Franklingo13/Efecto-dopler/Piezas/medidas_pieza1.bmp

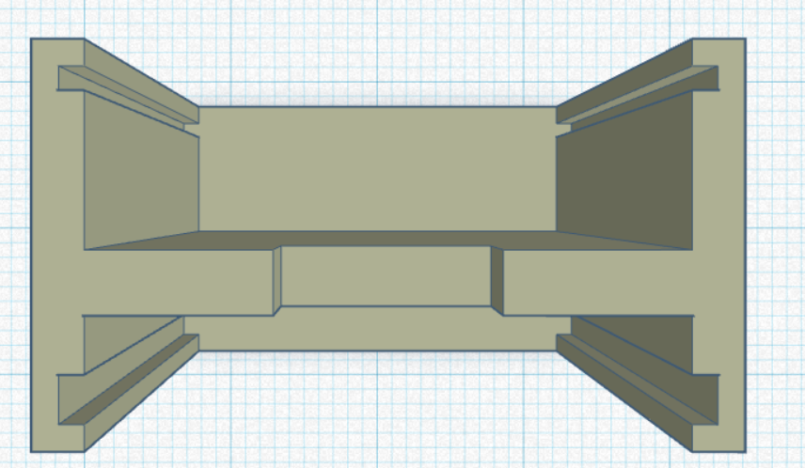
Piezas/medidas_pieza1.bmp
