Franklingo13/Efecto-dopler/Imágenes/prueba1_velocidad.png

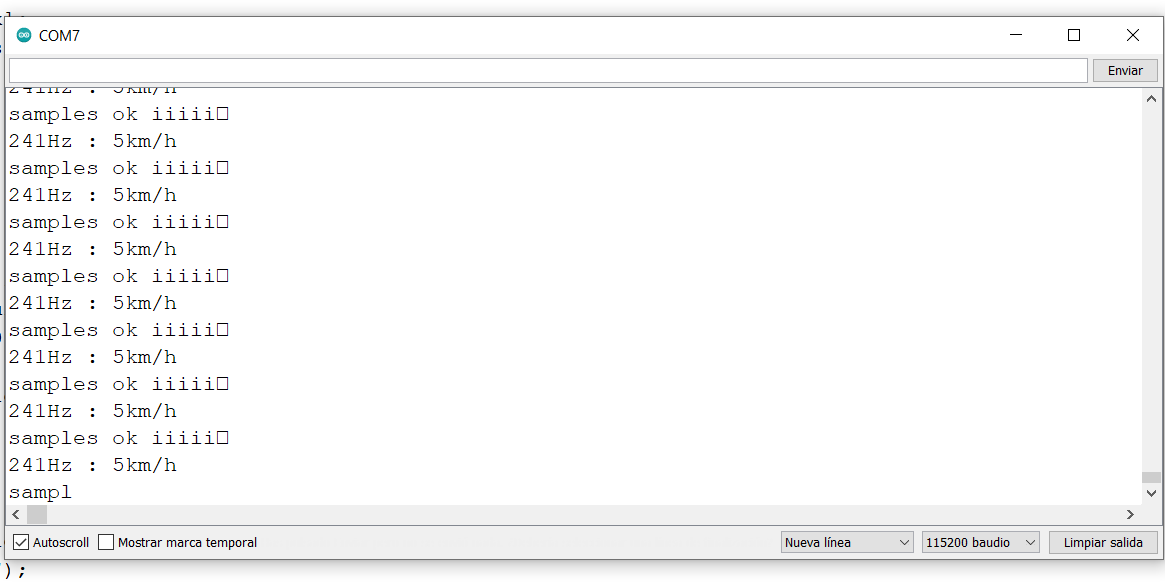
Imágenes/prueba1_velocidad.png
