Franklingo13/Efecto-dopler/cdm324_backpack-master/simus/cdm324-limpkin.asc

C1: cap; 10µ
C2: cap; 10µ
C3: cap; 220p
C4: cap; 220p
C5: cap; 10µ
R1: res; 4.7k
R2: res; 10k
R3: res; 10k
R5: res; 650k
R7: res; 4.7k
R8: res; 650k
R9: res; 4.7k
U3: LT1037
U4: LT1037
V1: voltage; 5; Rser=0
V2: voltage; ""; AC 1; Rser=0
Named nets: 0, IF, DOP_AMP
.ac oct 1000 0.1 30k
