Franklingo13/Efecto-dopler/cdm324_backpack-master/simus/cdm324-ebay.asc

C1: cap; 2.2µ
C2: cap; 10µ
C3: cap; 10n
C4: cap; 470p
C5: cap; 4.7µ
C7: cap; 1n
R1: res; 10k
R2: res; 10k
R3: res; 10k
R5: res; 510k
R7: res; 10k
R8: res; 1000k
R9: res; 1k
U3: LT1037
U4: LT1037
V1: voltage; 5; Rser=0
V2: voltage; ""; AC 1; Rser=0
Named nets: 0, IF, DOP_AMP
.ac oct 1000 0.1 30k
