Franklingo13/Efecto-dopler/cdm324_backpack-master/simus/transiente_limpkin.asc

C1: cap; 10µ
C2: cap; 10µ
C3: cap; 270p
C4: cap; 10µ
C5: cap; 270p
C6: cap; 10µ
R1: res; 10k
R2: res; 10k
R3: res; 590k
R4: res; 4.7k
R5: res; 590k
R6: res; 4.7k
R7: res; 4.7k
R8: res; 1k
R9: res; 20k
U1: LT1037
U2: LT1037
U3: LT1037
V1: voltage; 5; Rser=0
V3: voltage; SINE(0 60mV 4Khz)
Named nets: 0, IF, DOP_AMP, V1, Fout, Vref
.tran 0 8ms 5ms 10ms
